masiarhub/kicad_dummy_repo/HTML/images/cat_pdf_drill_map_ci_dummy-NPTH_drill_map.png

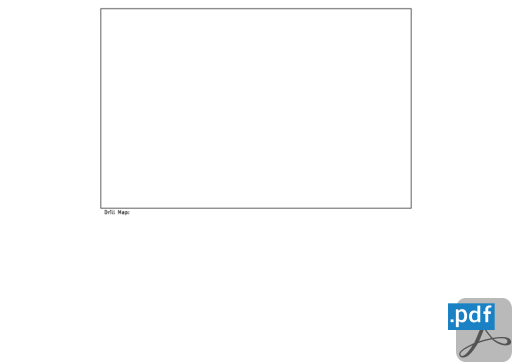
HTML/images/cat_pdf_drill_map_ci_dummy-NPTH_drill_map.png
