masiarhub/kicad_dummy_repo/HTML/images/cat_png_3d_viewer_angled_top_ci_dummy-angled_top.png

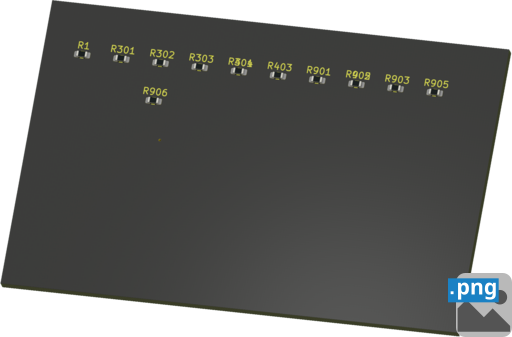
HTML/images/cat_png_3d_viewer_angled_top_ci_dummy-angled_top.png
