masiarhub/kicad_dummy_repo/HTML/images/cat_png_3d_viewer_bottom_ci_dummy-bottom.png

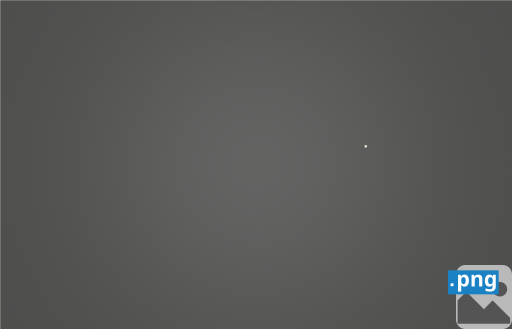
HTML/images/cat_png_3d_viewer_bottom_ci_dummy-bottom.png
