masiarhub/kicad_dummy_repo/Images/ci_dummy-top.png

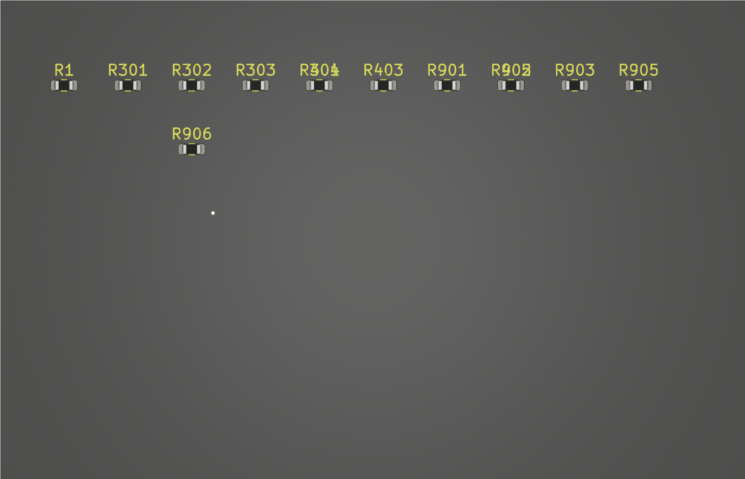
Images/ci_dummy-top.png
