masiarhub/kicad_dummy_repo/Manufacturing/Fabrication/ci_dummy-fabrication.pdf

# Top Fabrication (Scale 1:1)

# Board Name Fabrication Document

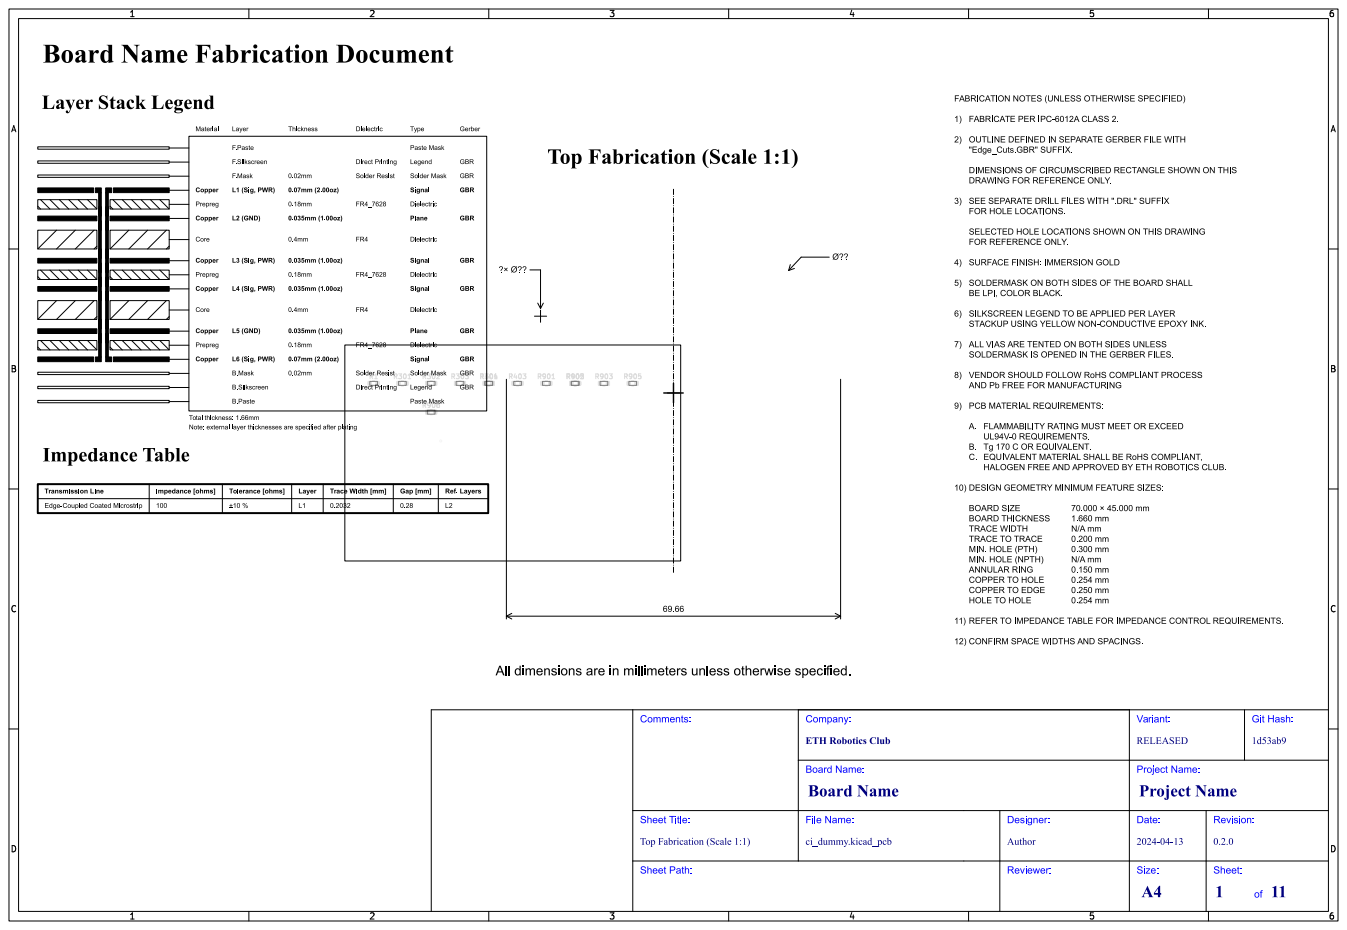
[picture p10: page 1]

# Bottom Fabrication (Scale 1:1)

# Board Name Fabrication Document

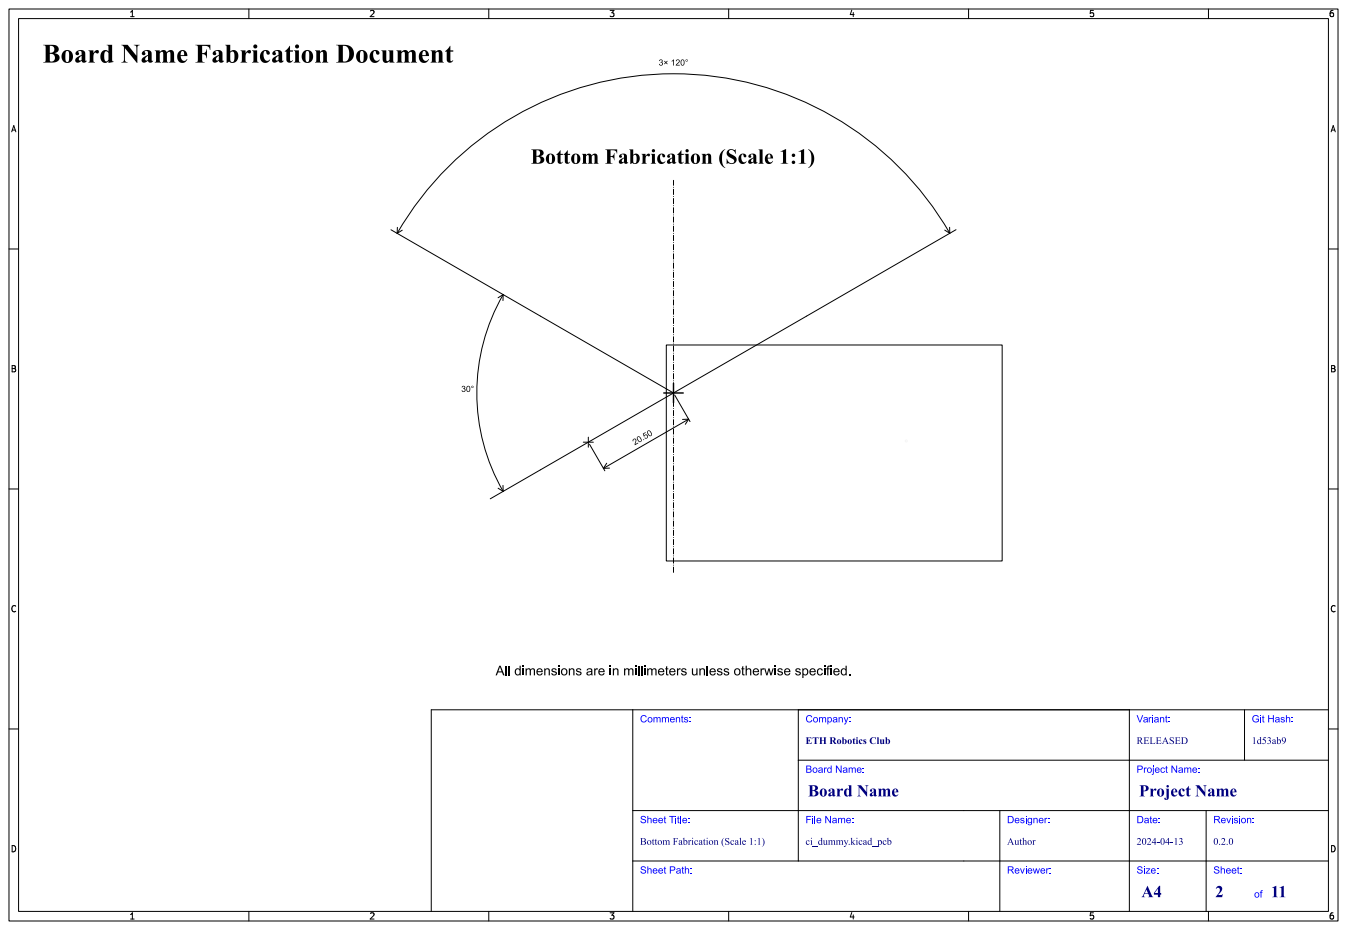
[picture p11: page 2]
Git; Hash:; Comments:; Sheet Path:; Sheet Title:; File Name:; Board Name; Project Name; Company:; RELEASED; Variant:; Board Name:; ci_dummy.kicad_pcb; Author; Designer:; Reviewer:; Project Name:; Date:; Revision:; Size:; Sheet:

ETH Robotics Club

Bottom Fabrication (Scale 1:1)

# Drill Drawing L1 - L6 (Scale 1:1)

# Board Name Fabrication Document

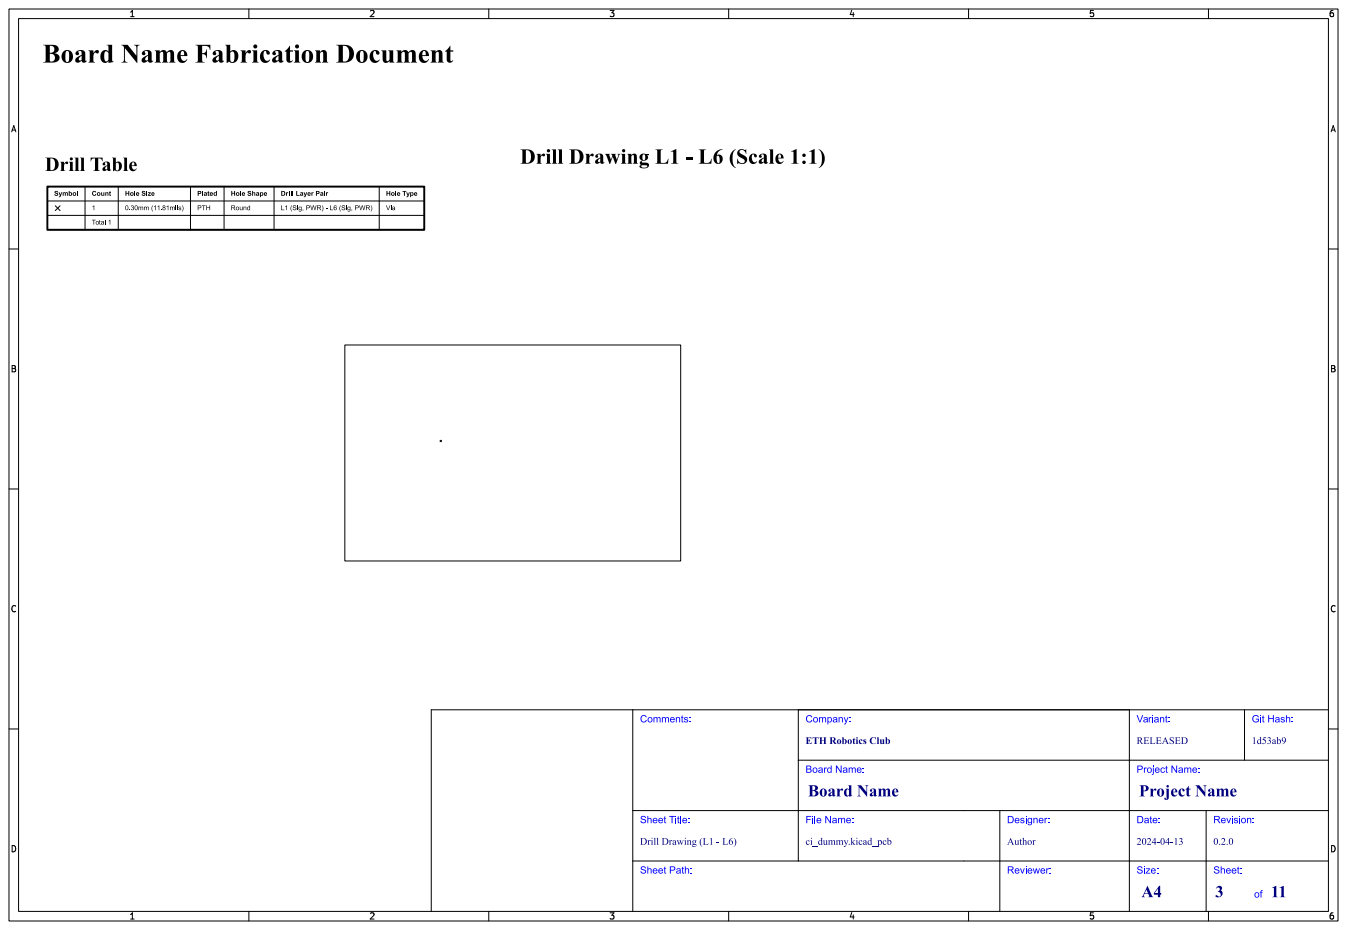
[picture p12: page 3]
Git; Hash:; Comments:; Drill Drawing (L1 - L6); Sheet Path:; Sheet Title:; File Name:; Board Name; Project Name; Company:; RELEASED; Variant:; Board Name:; ci_dummy.kicad_pcb; Author; Designer:; Reviewer:; Project Name:; Date:; Revision:; Size:; Sheet:

ETH Robotics Club

# Top Test Points (Scale 1:1)

# Board Name Fabrication Document

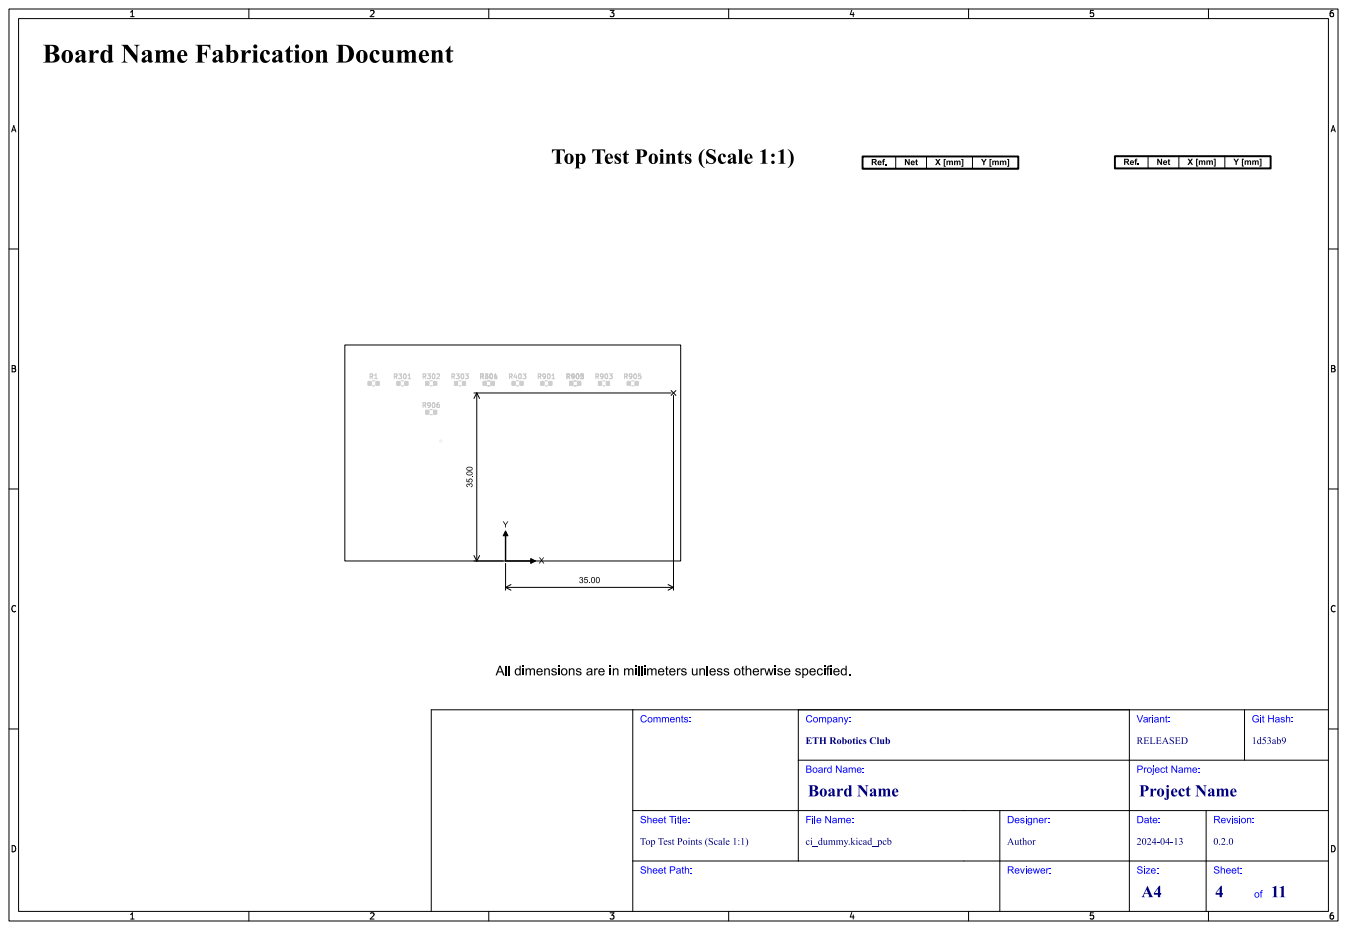
[picture p13: page 4]

Top Test Points (Scale 1:1)

# Bottom Test Points (Scale 1:1)

# Board Name Fabrication Document

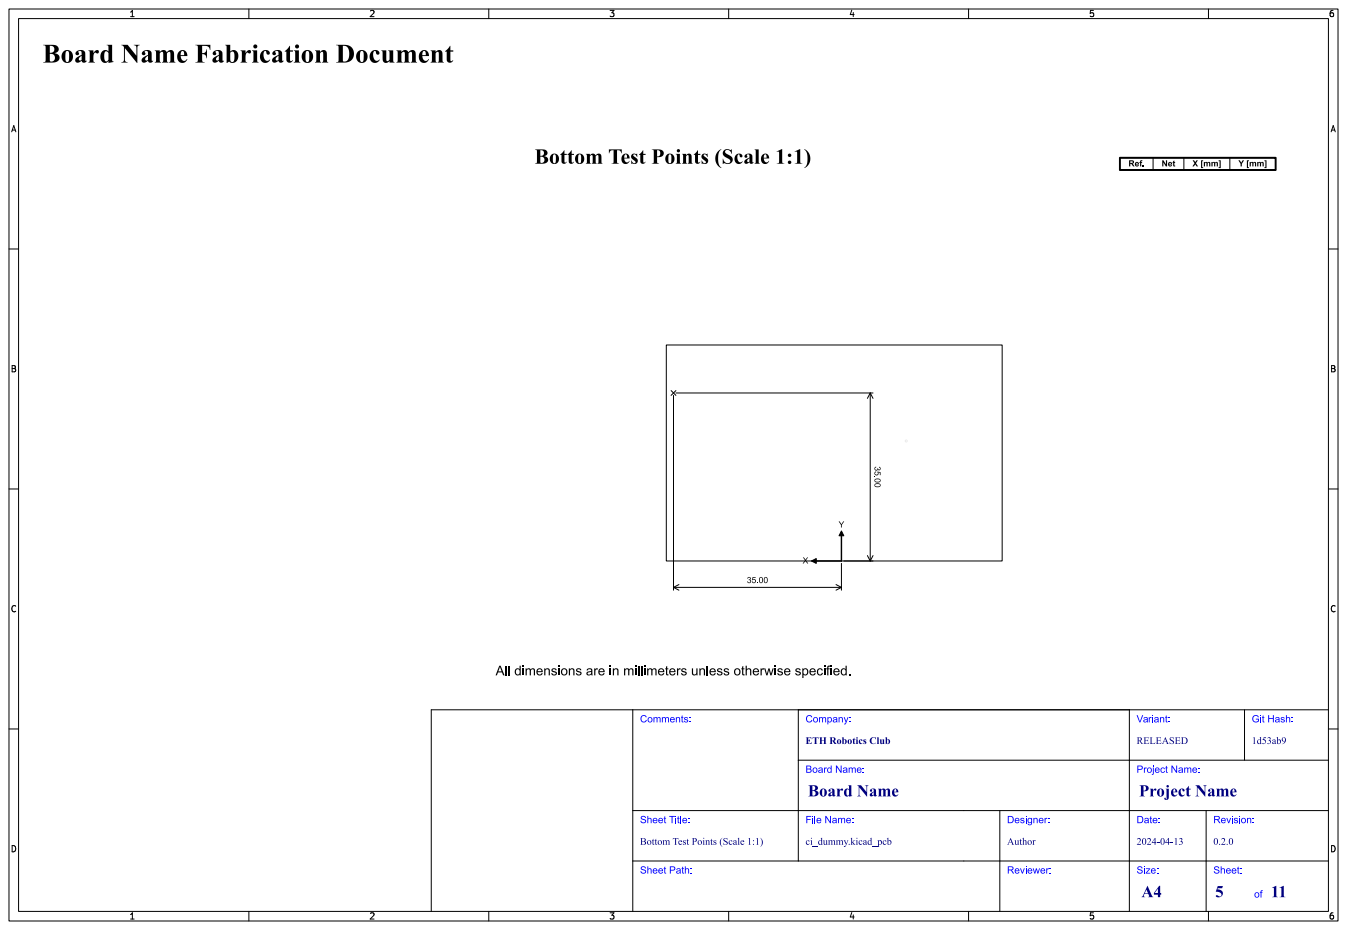
[picture p14: page 5]
Git; Hash:; Comments:; Sheet Path:; Sheet Title:; File Name:; Board Name; Project Name; Company:; RELEASED; Variant:; Board Name:; ci_dummy.kicad_pcb; Author; Designer:; Reviewer:; Project Name:; Date:; Revision:; Size:; Sheet:

ETH Robotics Club

Bottom Test Points (Scale 1:1)

# L1 (Sig, PWR) (Scale 1:1)

# Board Name Fabrication Document

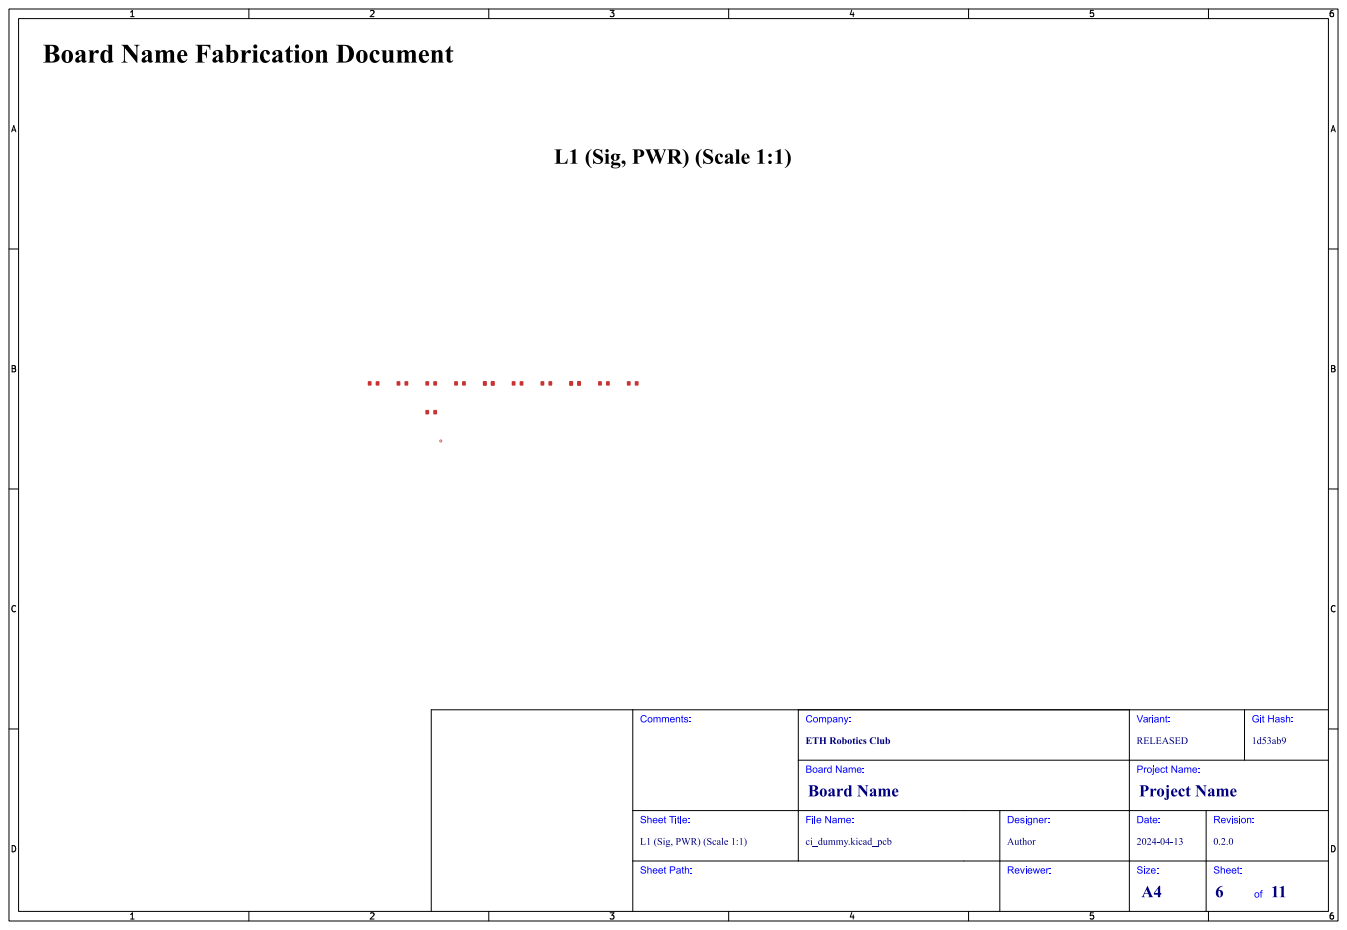
[picture p15: page 6]
Git; Hash:; Comments:; Sheet Path:; Sheet Title:; File Name:; Board Name; Project Name; Company:; RELEASED; Variant:; Board Name:; ci_dummy.kicad_pcb; Author; Designer:; Reviewer:; Project Name:; Date:; Revision:; Size:; Sheet:

ETH Robotics Club

L1 (Sig, PWR) (Scale 1:1)

# L2 (GND) (Scale 1:1)

# Board Name Fabrication Document

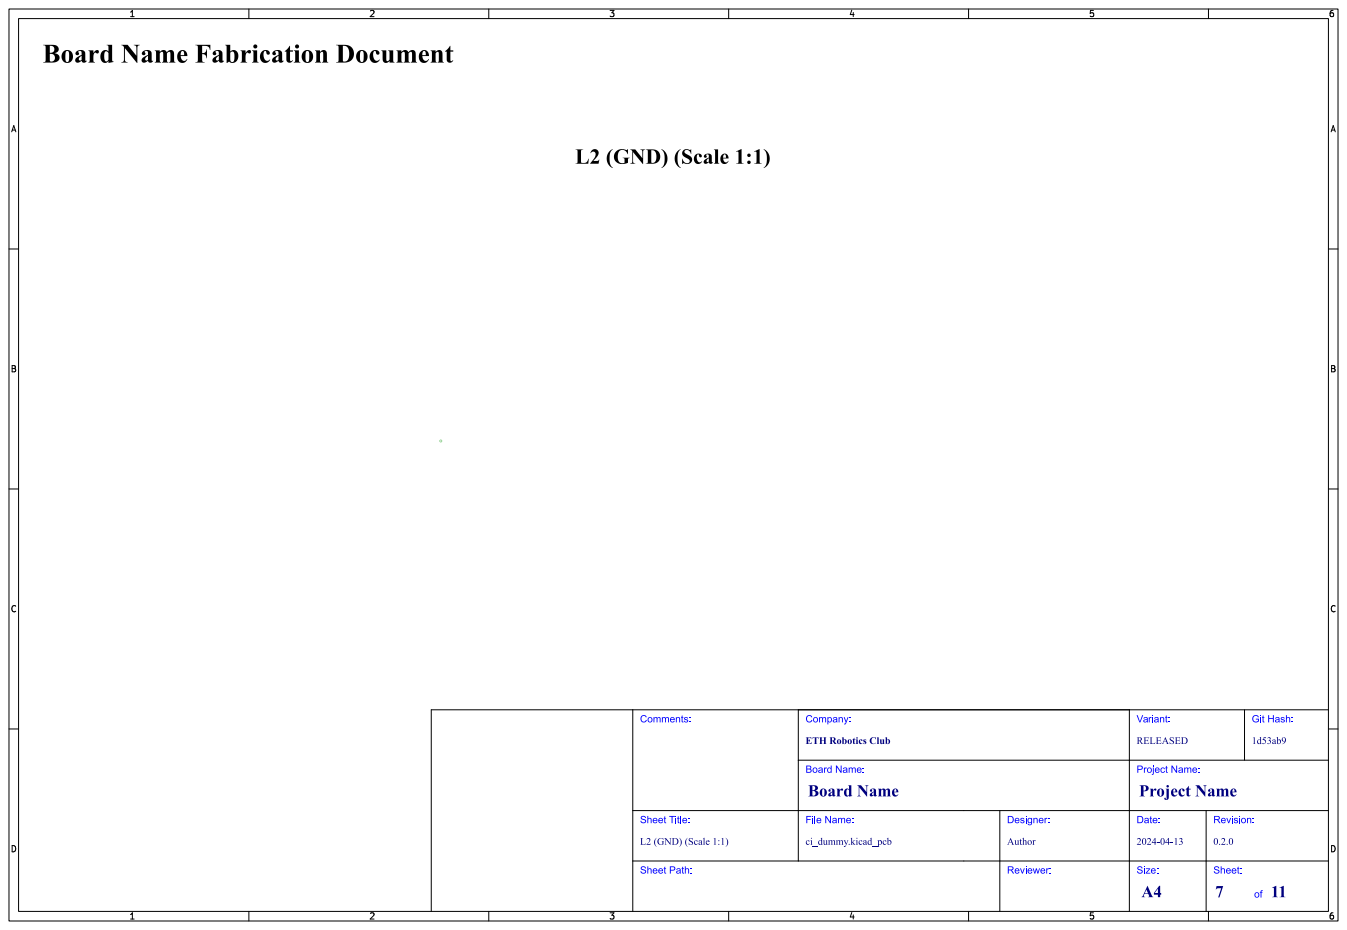
[picture p16: page 7]
Git; Hash:; Comments:; L2 (GND) (Scale 1:1); Sheet Path:; Sheet Title:; File Name:; Board Name; Project Name; Company:; RELEASED; Variant:; Board Name:; ci_dummy.kicad_pcb; Author; Designer:; Reviewer:; Project Name:; Date:; Revision:; Size:; Sheet:

ETH Robotics Club

# L3 (Sig, PWR) (Scale 1:1)

# Board Name Fabrication Document

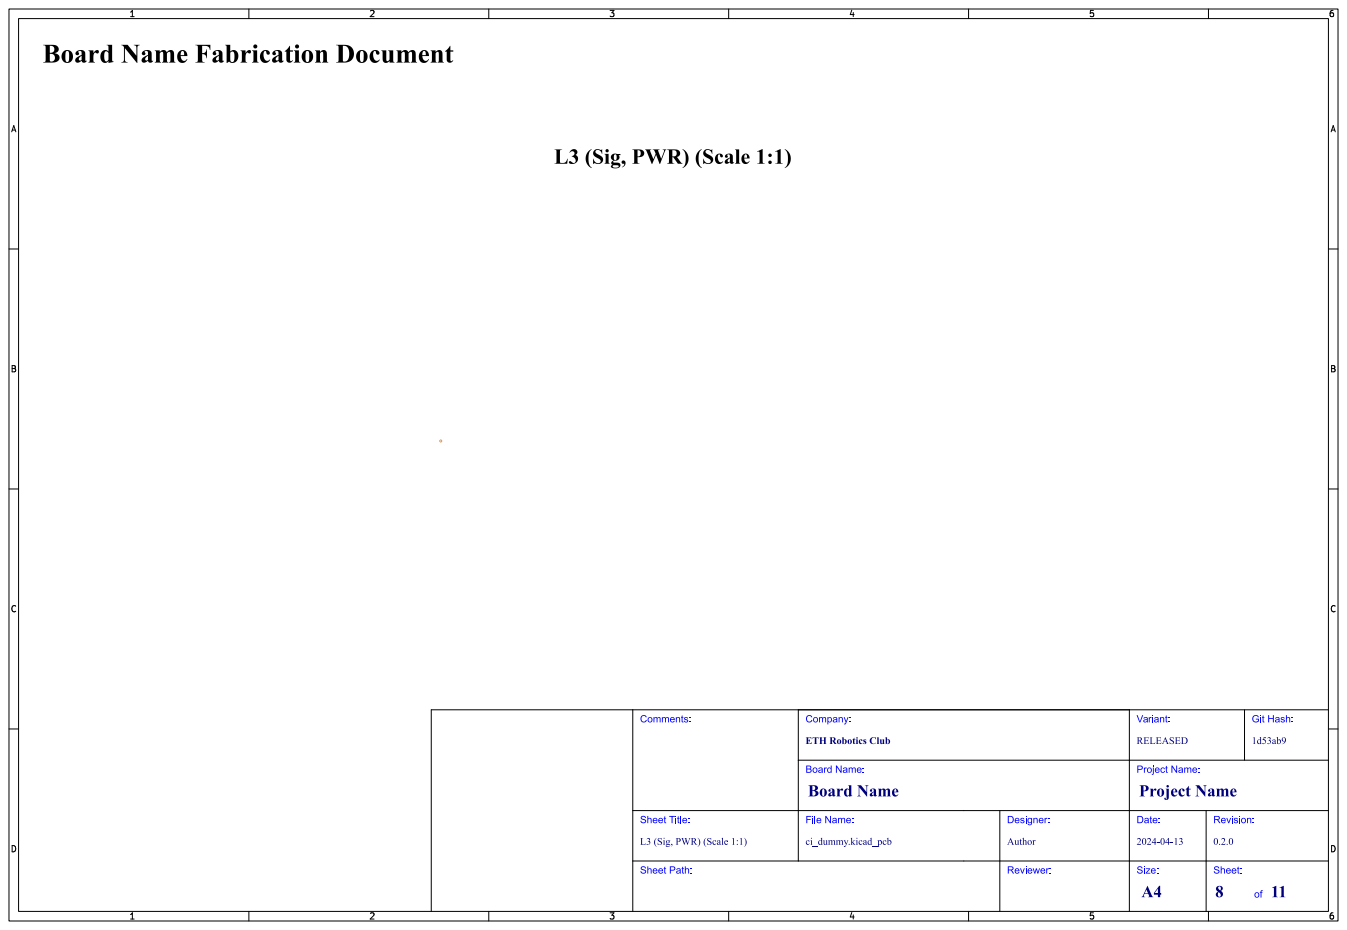
[picture p17: page 8]
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

ETH Robotics Club

L3 (Sig, PWR) (Scale 1:1)

# L4 (Sig, PWR) (Scale 1:1)

# Board Name Fabrication Document

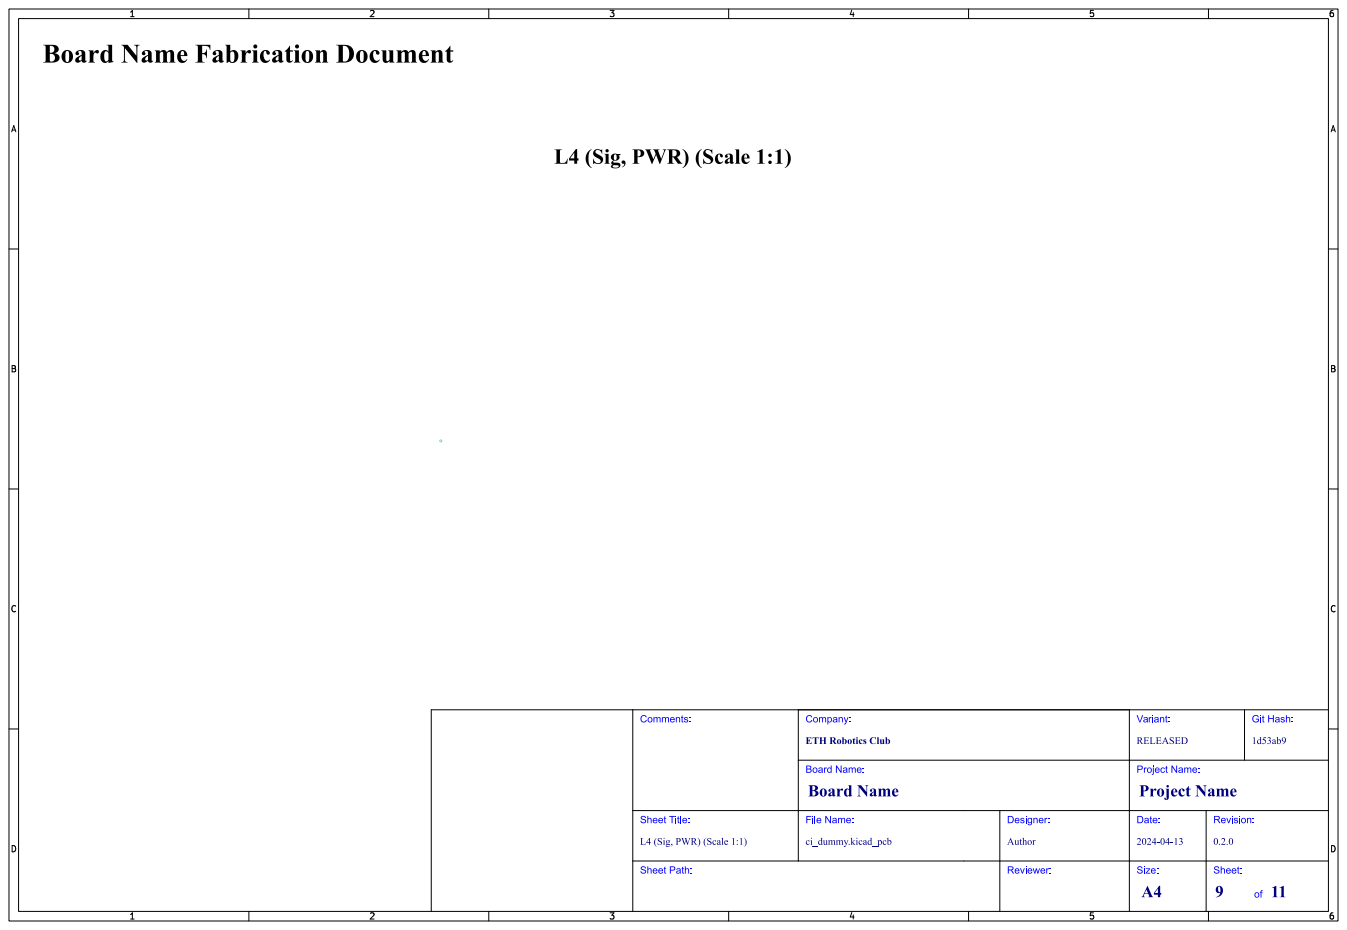
[picture p18: page 9]
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

ETH Robotics Club

L4 (Sig, PWR) (Scale 1:1)

# L5 (GND) (Scale 1:1)

# Board Name Fabrication Document

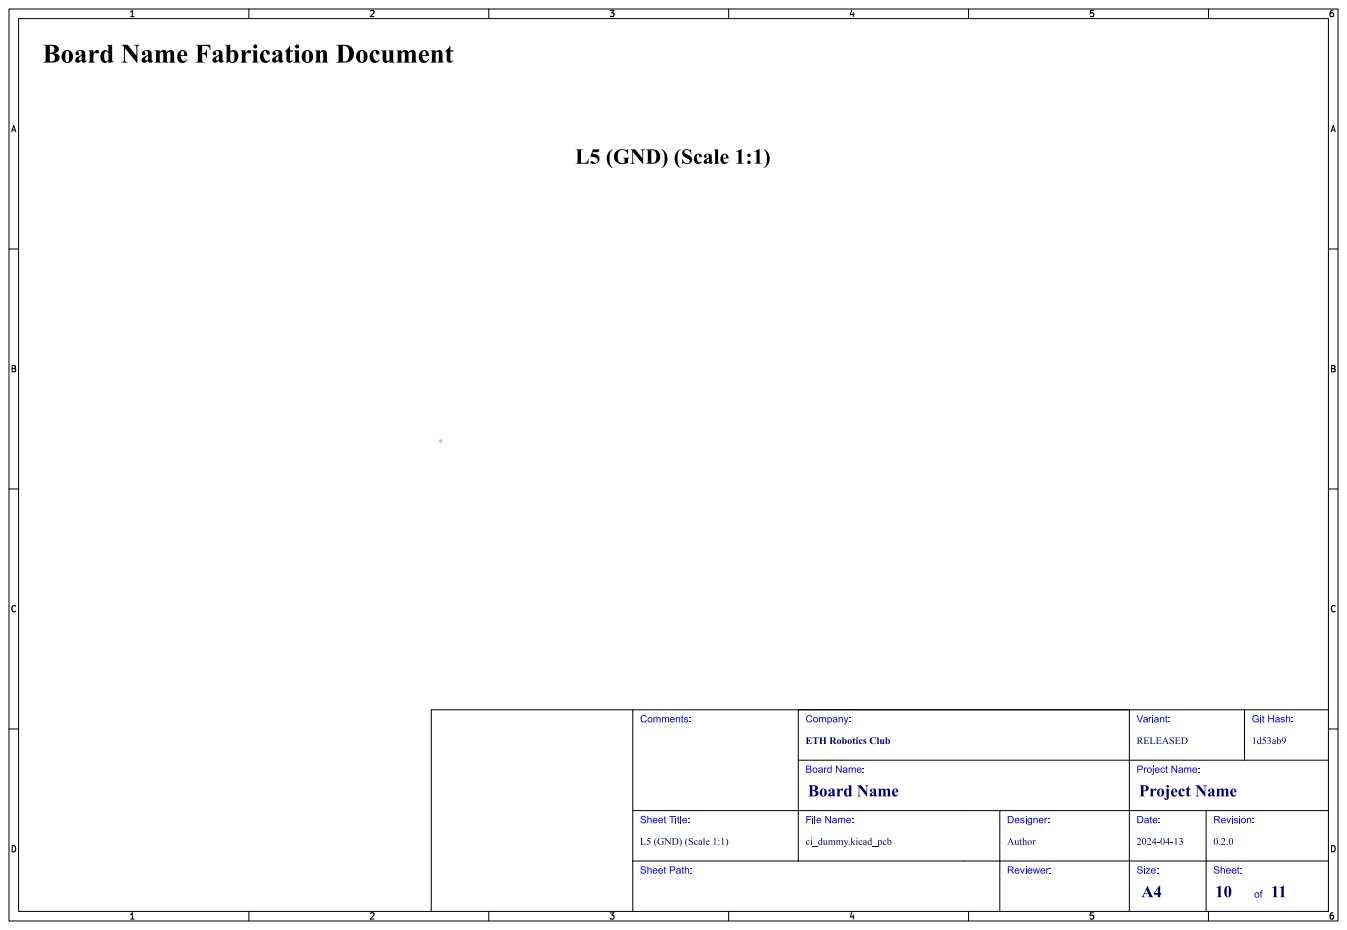
[picture p19: page 10]
Git; Hash:; Comments:; L5 (GND) (Scale 1:1); Sheet Path:; Sheet Title:; File Name:; Board Name; Project Name; Company:; RELEASED; Variant:; Board Name:; ci_dummy.kicad_pcb; Author; Designer:; Reviewer:; Project Name:; Date:; Revision:; Size:; Sheet:

ETH Robotics Club

# L6 (Sig, PWR) (Scale 1:1)

# Board Name Fabrication Document

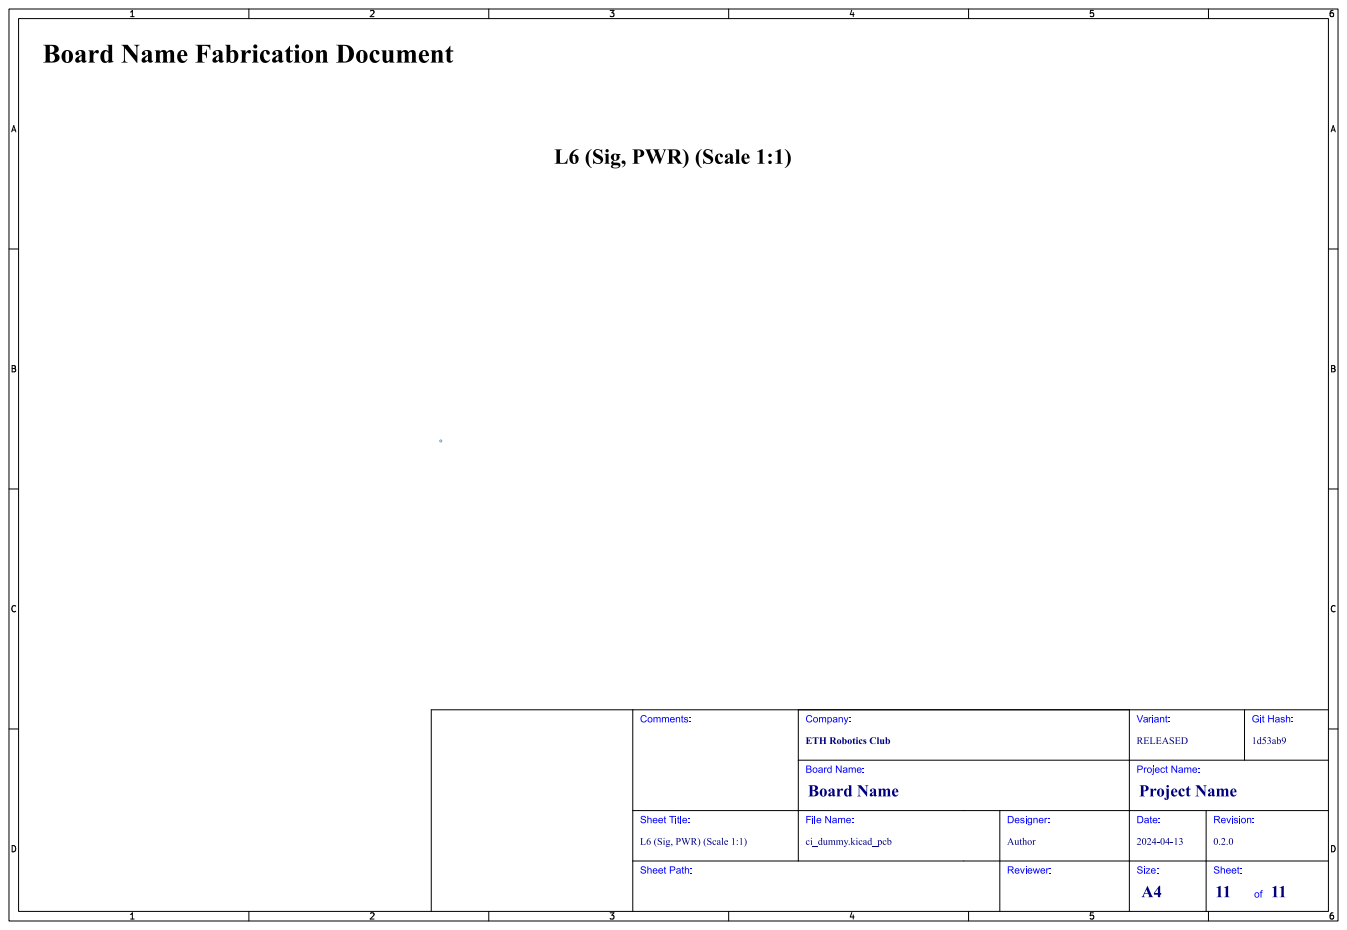
[picture p20: page 11]
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

ETH Robotics Club

L6 (Sig, PWR) (Scale 1:1)
