masiarhub/kicad_dummy_repo/Manufacturing/Fabrication/ci_dummy-fabrication-1.pdf

# Top Fabrication (Scale 1:1)

# Board Name Fabrication Document
