masiarhub/kicad_dummy_repo/Manufacturing/Fabrication/ci_dummy-fabrication-4.pdf

# Top Test Points (Scale 1:1)

# Board Name Fabrication Document


Top Test Points (Scale 1:1)
