masiarhub/kicad_dummy_repo/Manufacturing/Fabrication/ci_dummy-fabrication-9.pdf

# L4 (Sig, PWR) (Scale 1:1)

# Board Name Fabrication Document

Git; Hash:; Comments:; Sheet Path:; Sheet Title:; File Name:; Board Name; Project Name; Company:; RELEASED; Variant:; Board Name:; ci_dummy.kicad_pcb; Author; Designer:; Reviewer:; Project Name:; Date:; Revision:; Size:; Sheet: 9

ETH Robotics Club

L4 (Sig, PWR) (Scale 1:1)
