masiarhub/kicad_dummy_repo/Manufacturing/Fabrication/Gerbers/ci_dummy-NPTH_drill_map.pdf

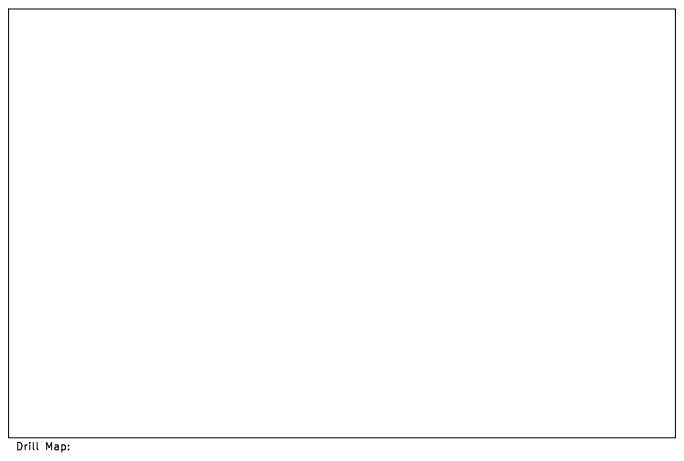
[picture p33: page 1]
