masiarhub/kicad_dummy_repo/Manufacturing/Fabrication/Gerbers/ci_dummy-PTH_drill_map.pdf

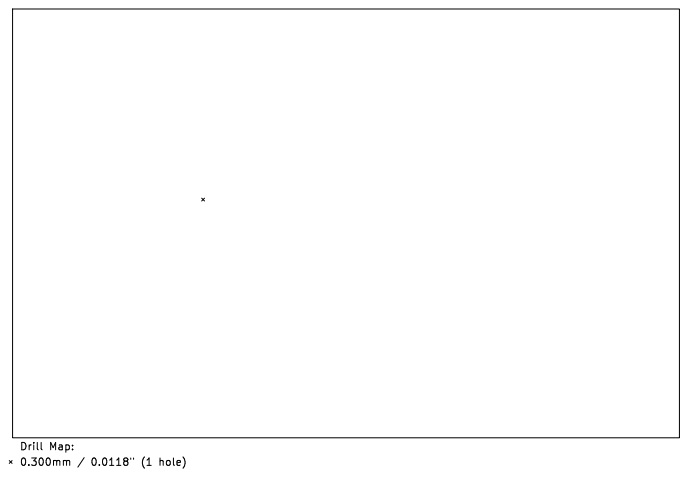
[picture p34: page 1]
