masiarhub/kicad_dummy_repo/Project Architecture.kicad_sch

## KiCad design Project Architecture.kicad_sch (2026-10-10)

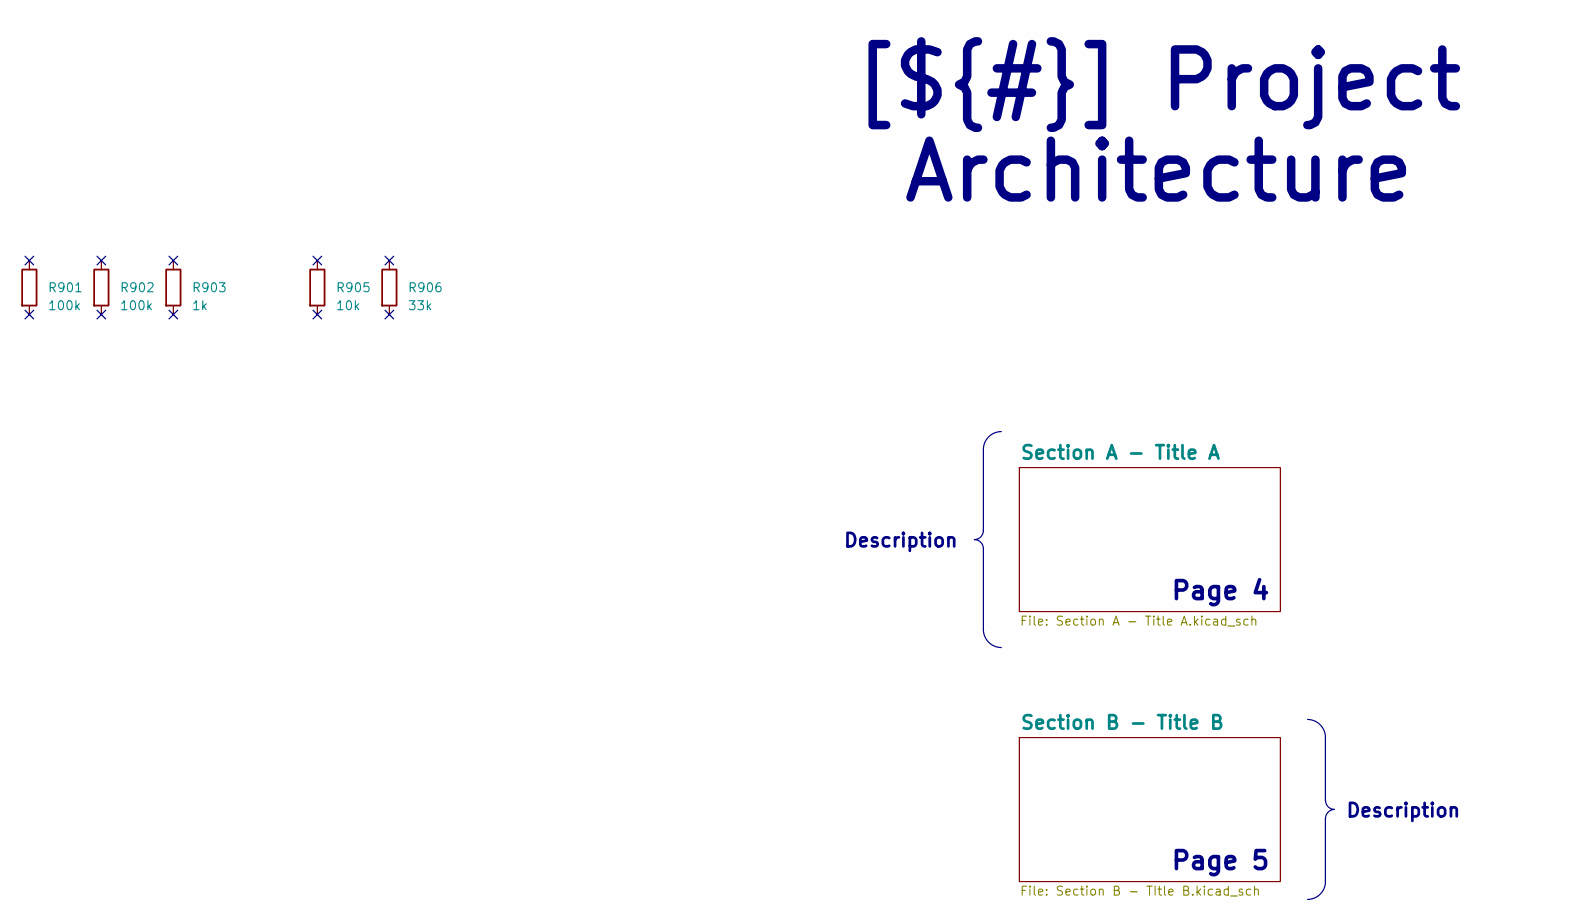
[picture p35: schematic Project Architecture.kicad_sch]

Parts:
R901, R902: 100k; R_0603_1608Metric
R903: 1k; R_0603_1608Metric
R905: 10k; R_0603_1608Metric
R906: 33k; R_0603_1608Metric

Notes on the sheet:
Description
[${#}] ${TITLE}
Page 5
Page 4
