masiarhub/kicad_dummy_repo/Section A - Title A.kicad_sch

## KiCad design Section A - Title A.kicad_sch (2026-10-10)

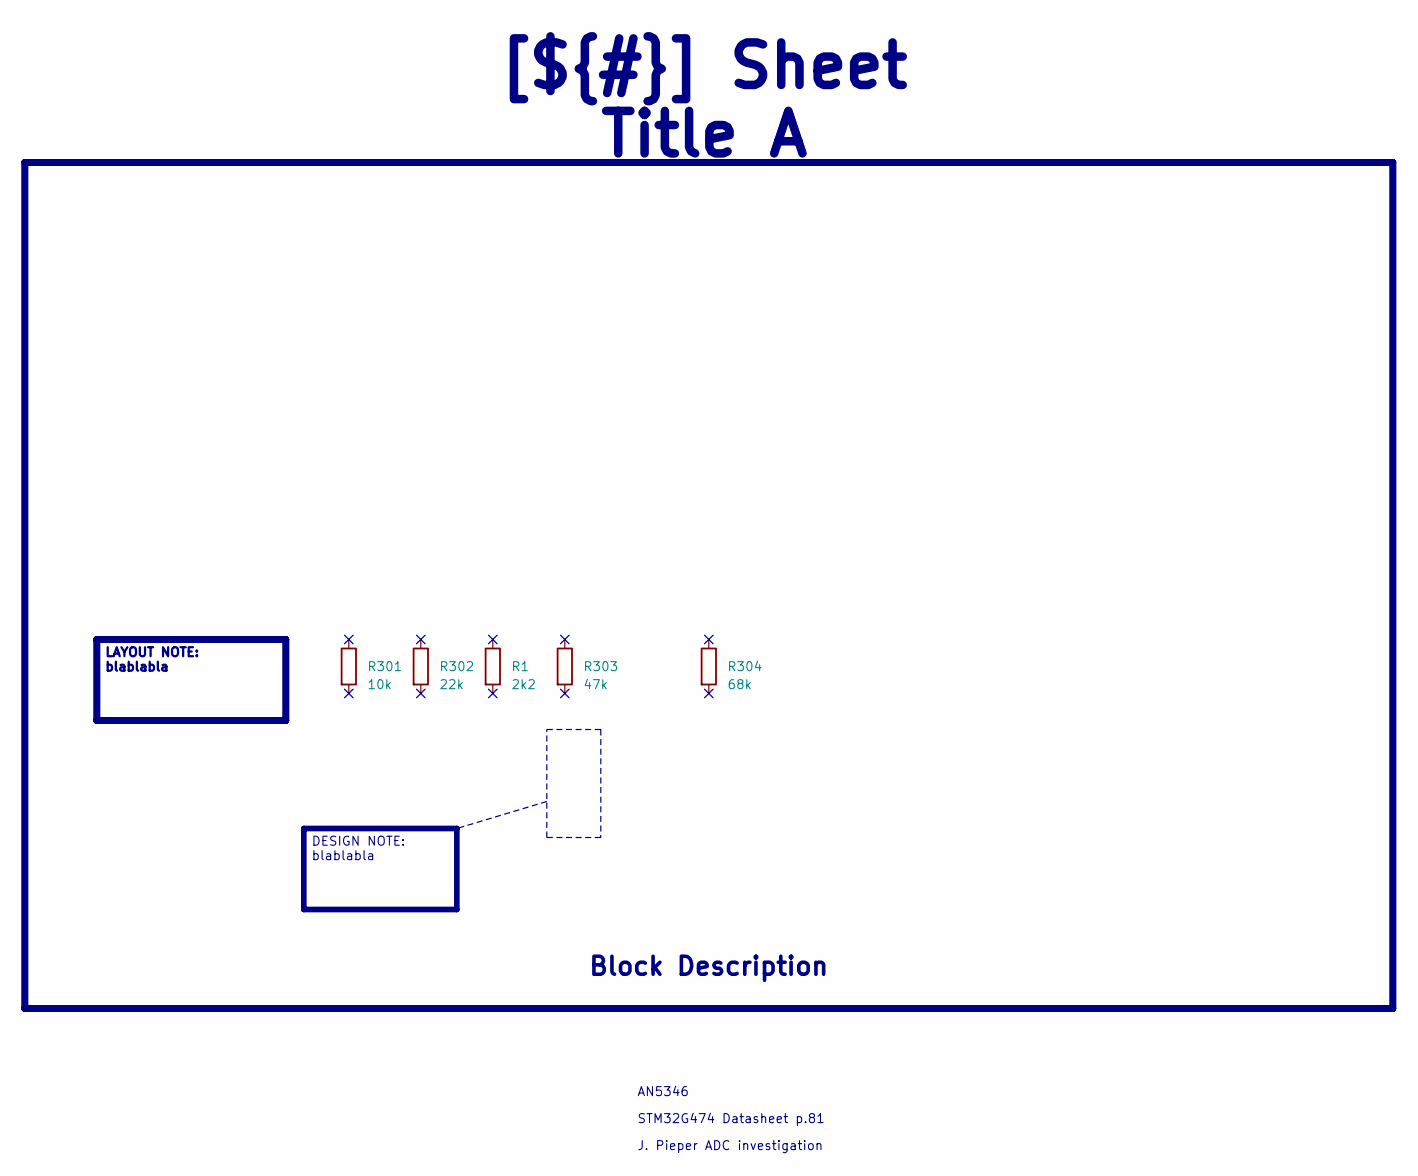
[picture p36: schematic Section A - Title A.kicad_sch]

Parts:
R1: 2k2; R_0603_1608Metric
R301: 10k; R_0603_1608Metric
R302: 22k; R_0603_1608Metric
R303: 47k; R_0603_1608Metric
R304: 68k; R_0603_1608Metric

Notes on the sheet:
LAYOUT NOTE: blablabla
[${#}] ${TITLE}
Block Description
DESIGN NOTE: blablabla
J. Pieper ADC investigation
STM32G474 Datasheet p.81
AN5346
