masiarhub/kicad_dummy_repo/Section B - TItle B.kicad_sch

## KiCad design Section B - TItle B.kicad_sch (2026-10-10)

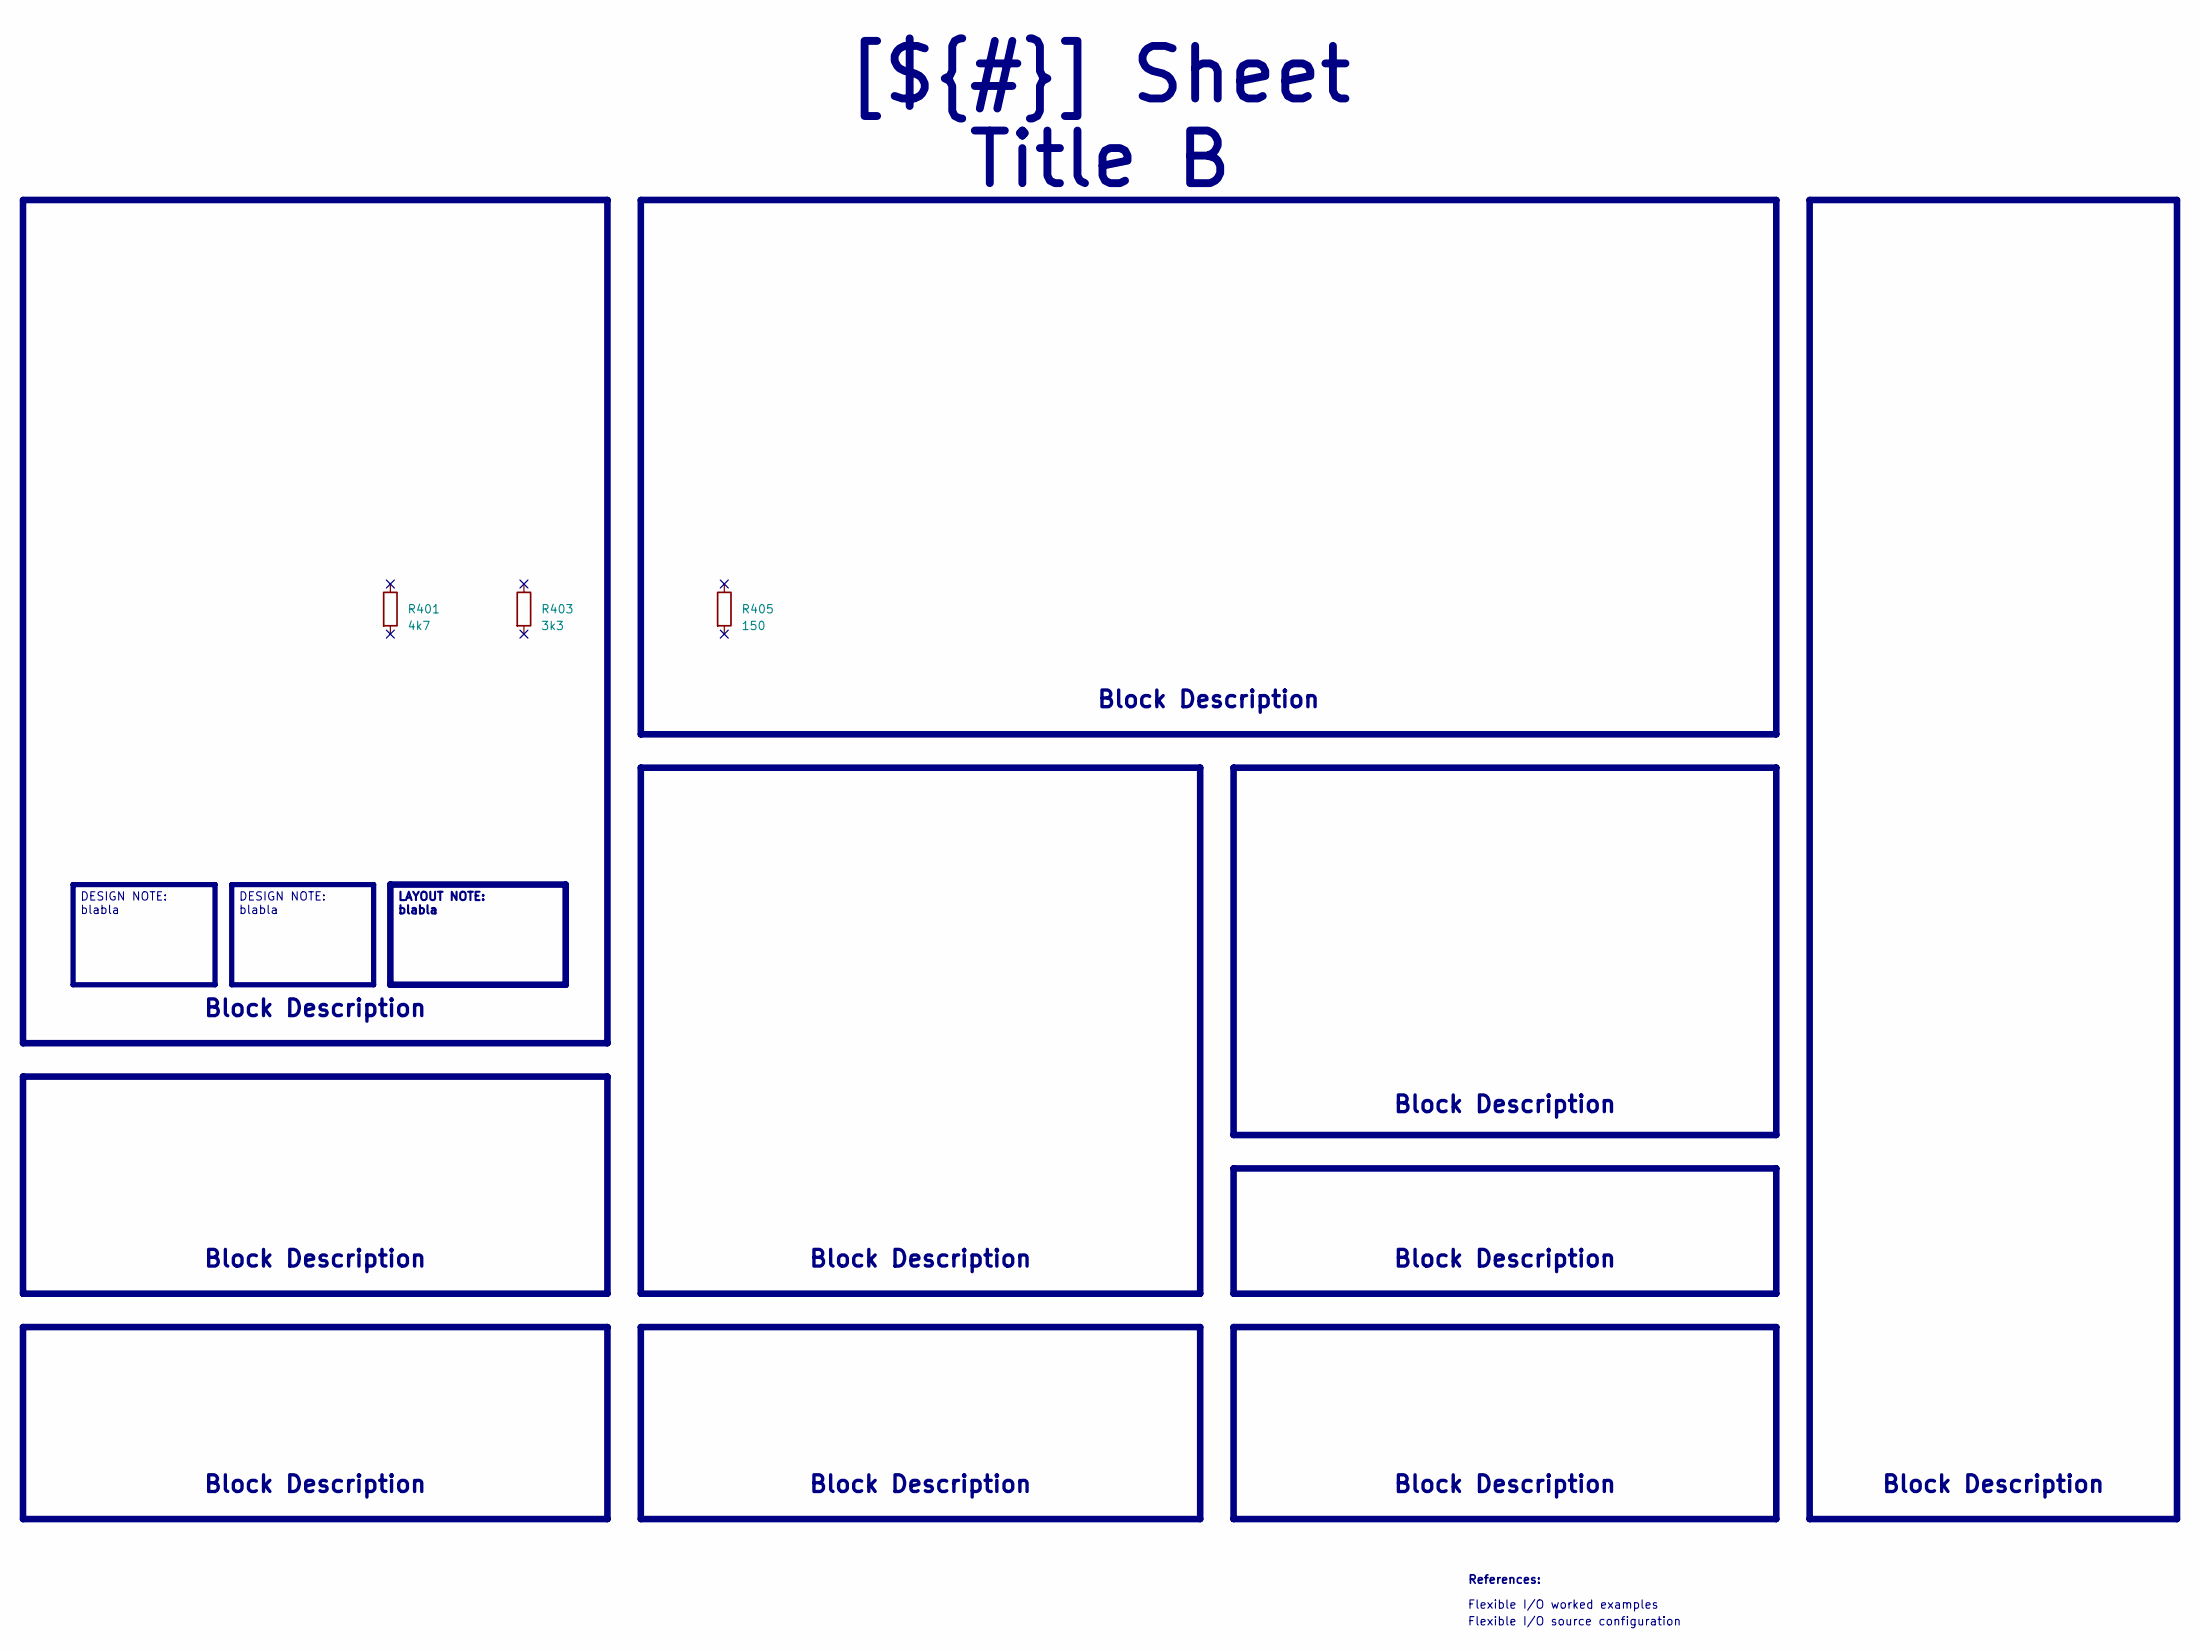
[picture p37: schematic Section B - TItle B.kicad_sch]

Parts:
R401: 4k7; R_0603_1608Metric
R403: 3k3; R_0603_1608Metric
R405: 150; R_0603_1608Metric

Notes on the sheet:
Block Description
[${#}] ${TITLE}
DESIGN NOTE: blabla
LAYOUT NOTE: blabla
Flexible I/O worked examples
References:
Flexible I/O source configuration
